ramonimbao/stm32_watch/hardware/board/ButtonDebounce.asc

C1: cap; 1µ
C2: cap; 10µ
C3: cap; 100n
C4: cap; 100n
R1: res; 10k
R2: res; 1k
R3: res; 1k
R4: res; 10k
V1: voltage; PULSE(0 3.3 1m 10n 10n 100u 200u 50)
V2: voltage; PULSE(0 3.3 1m 10n 10n 100u 200u 50)
V3: voltage; PULSE(0 3.3 1m 10n 10n 100u 200u 50)
V4: voltage; PULSE(0 3.3 1m 10n 10n 100u 200u 50)
V5: voltage; PWL(0 0 11.0199m 0 11.02m 3.3)
V6: voltage; PWL(0 0 11.0199m 0 11.02m 3.3)
V7: voltage; PWL(0 0 11.0199m 0 11.02m 3.3)
V8: voltage; PWL(0 0 11.0199m 0 11.02m 3.3)
Named nets: 0, 10kR+100nC, 1kR+100nC, 10kR+1uC, 1kR+10uC
.tran 0 50m 0 0.1m
