ramonimbao/stm32_watch/software/Inc/inittriglut.h

/*
 * inttriglut.h
 *
 *  Created on: Dec 16, 2016
 *      Author: ramon
 */

#ifndef INTTRIGLUT_H_
#define INTTRIGLUT_H_

const int16_t SIN_LUT[] = {
	0,3425,6812,10125,13327,16383,19259,21925,24350,26509,28377,29934,31163,32050,32587,32767,32587,32050,31163,29934,28377,26509,24350,21925,19259,16383,13327,10125,6812,3425,0,-3426,-6813,-10126,-13328,-16384,-19260,-21926,-24351,-26510,-28378,-29935,-31164,-32051,-32588,-32767,-32588,-32051,-31164,-29935,-28378,-26510,-24351,-21926,-19260,-16384,-13328,-10126,-6813,-3426
};

const int16_t COS_LUT[] = {
	32767,32587,32050,31163,29934,28377,26509,24350,21925,19259,16383,13327,10125,6812,3425,0,-3426,-6813,-10126,-13328,-16384,-19260,-21926,-24351,-26510,-28378,-29935,-31164,-32051,-32588,-32767,-32588,-32051,-31164,-29935,-28378,-26510,-24351,-21926,-19260,-16384,-13328,-10126,-6813,-3426,-1,3425,6812,10125,13327,16383,19259,21925,24350,26509,28377,29934,31163,32050,32587,
};

int16_t i16_sin(int16_t degrees) {
	while (degrees < 0 || degrees > 359) {
		if (degrees < 0)
			degrees += 360;
		else if (degrees > 359)
			degrees -= 360;
	}
	return SIN_LUT[degrees / 6];
}

int16_t i16_cos(int16_t degrees) {
	while (degrees < 0 || degrees > 359) {
		if (degrees < 0)
			degrees += 360;
		else if (degrees > 359)
			degrees -= 360;
	}
	return COS_LUT[degrees / 6];
}

#endif /* INTTRIGLUT_H_ */
